CodeMarker01/do-an-1-b/Design Hardware/Design/Schematic.jpg

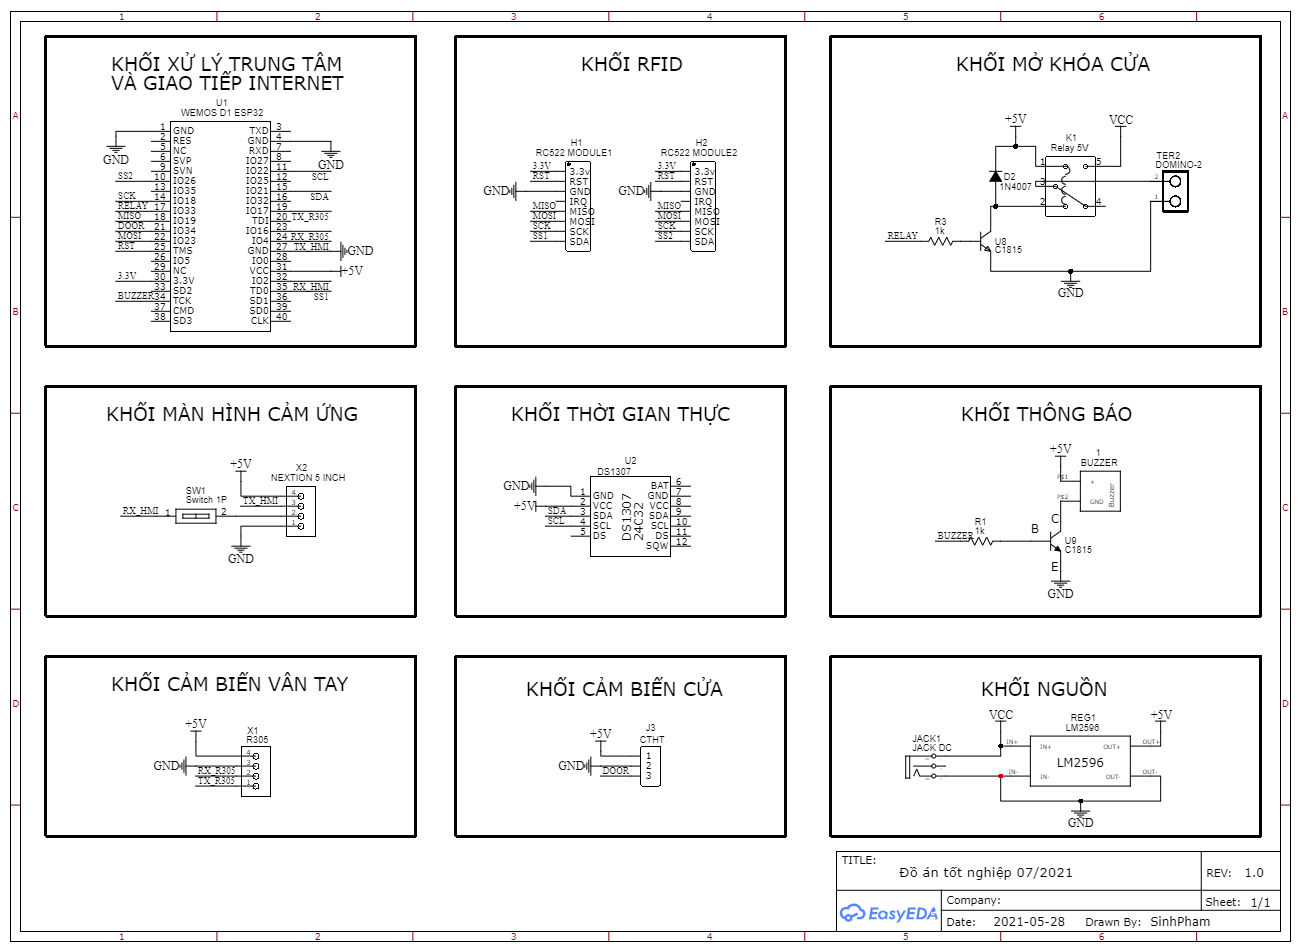
Design Hardware/Design/Schematic.jpg
