CodeMarker01/do-an-1-b/Design Hardware/Image/Actual image/z2544615937646_9335fb49bdb557f8bc9e90b8a1676609.jpg

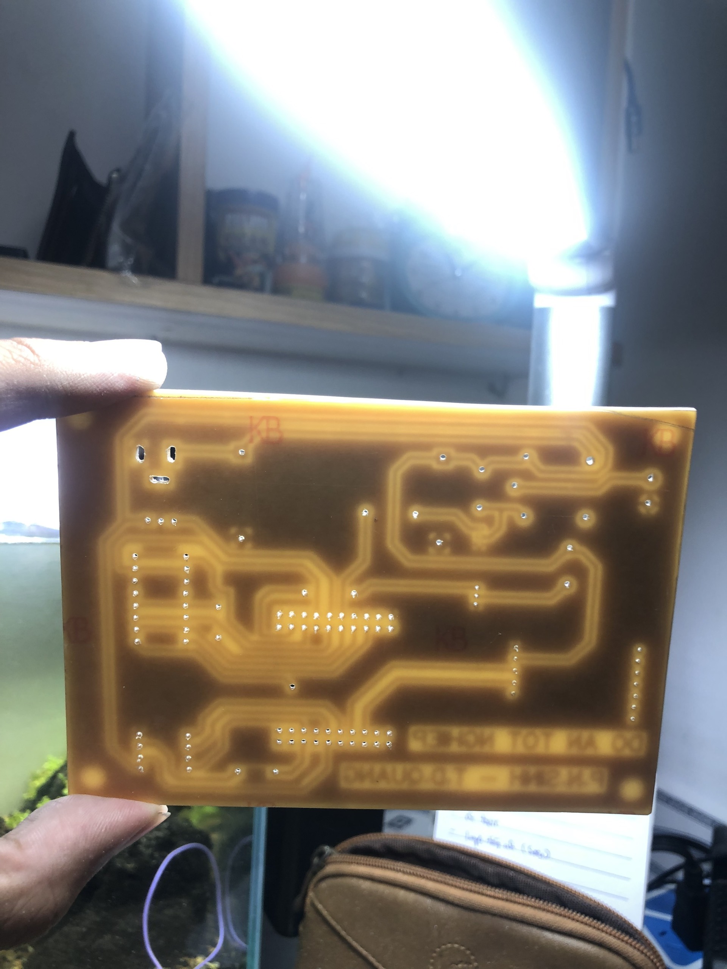
Design Hardware/Image/Actual image/z2544615937646_9335fb49bdb557f8bc9e90b8a1676609.jpg
