CodeMarker01/do-an-1-b/Design Hardware/Image/Actual image/z2544616110055_0c806b30d1a9bc31b851866c3de1ba1b.jpg

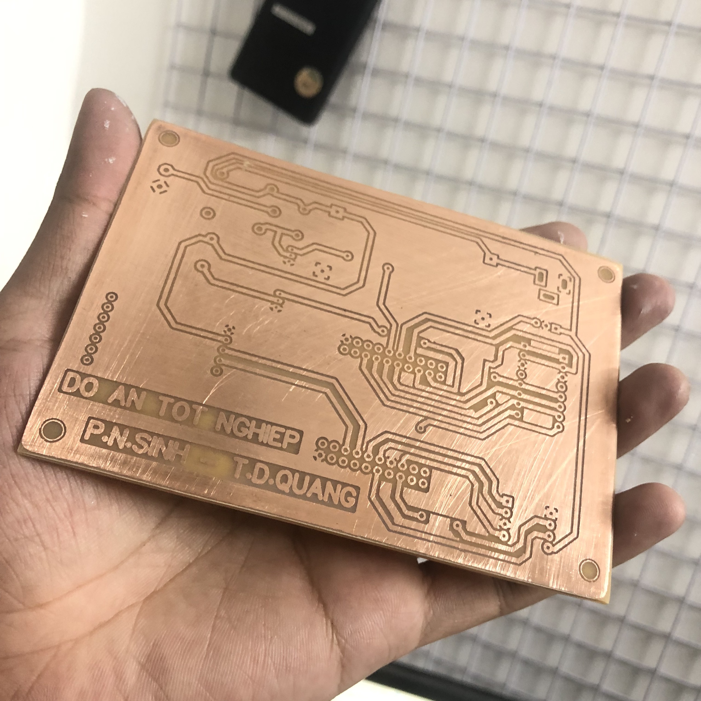
Design Hardware/Image/Actual image/z2544616110055_0c806b30d1a9bc31b851866c3de1ba1b.jpg
