CodeMarker01/do-an-1-b/Design Hardware/Image/Actual image/z2544616175655_86c2982712d3af7087d2432e3efe20b5.jpg

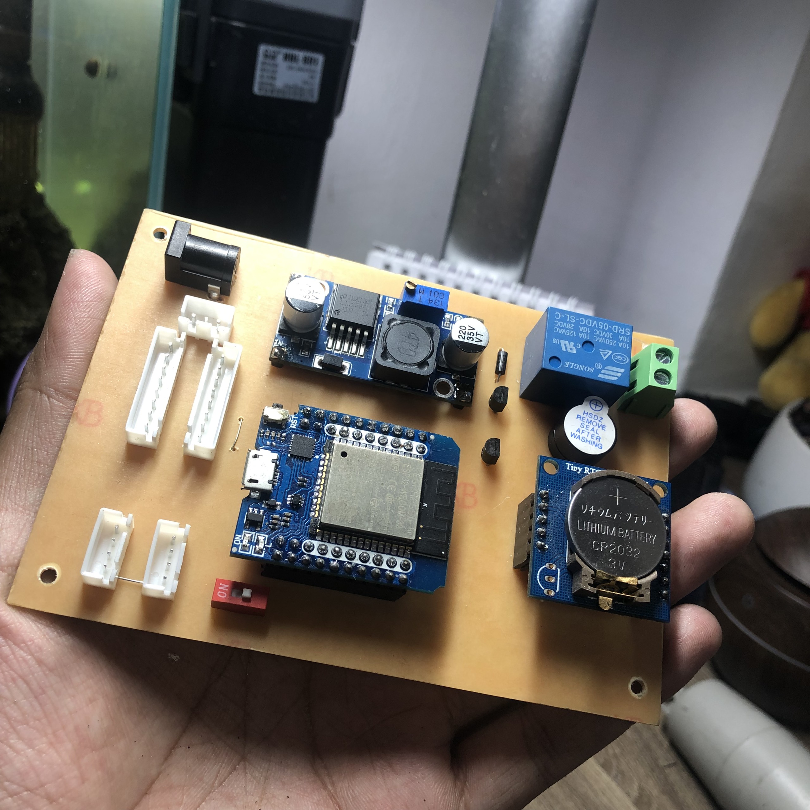
Design Hardware/Image/Actual image/z2544616175655_86c2982712d3af7087d2432e3efe20b5.jpg
