CodeMarker01/do-an-1-b/Design Hardware/Image/Actual image/z2544616294131_eab570bc93009f2e7a02063649fb9a35.jpg

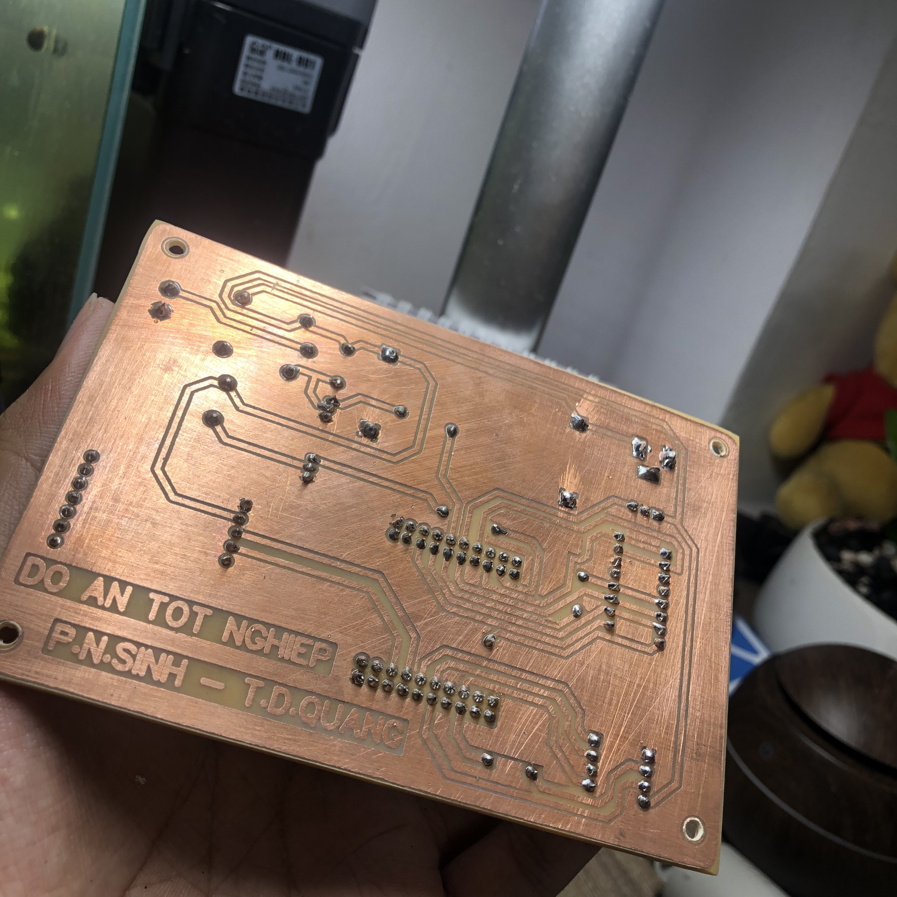
Design Hardware/Image/Actual image/z2544616294131_eab570bc93009f2e7a02063649fb9a35.jpg
