CodeMarker01/do-an-1-b/Design Hardware/Image/Actual image/z2544616418937_9a0d63e0b6e5f737682f1ef8a417e20c.jpg

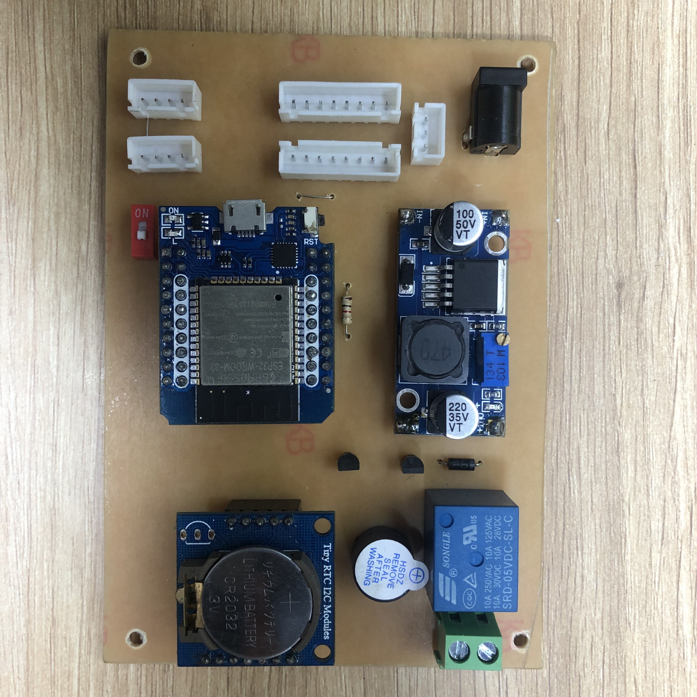
Design Hardware/Image/Actual image/z2544616418937_9a0d63e0b6e5f737682f1ef8a417e20c.jpg
