CodeMarker01/do-an-1-b/Design Hardware/Image/Actual image/z2544616560953_9db783ca1c101b86c6ae915941142b20.jpg

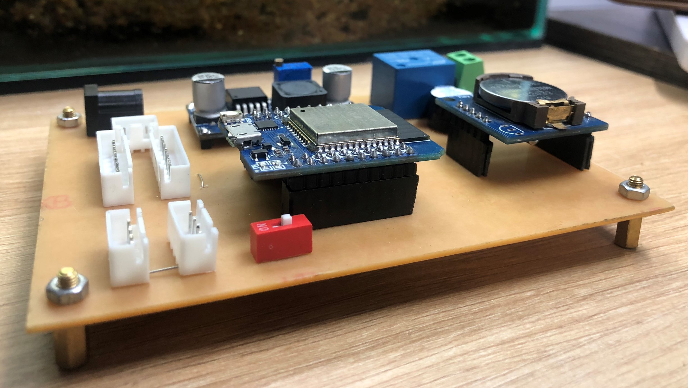
Design Hardware/Image/Actual image/z2544616560953_9db783ca1c101b86c6ae915941142b20.jpg
