CodeMarker01/do-an-1-b/Design Hardware/Image/Actual image/z2544616626180_2d66d4fd1934191050b84d0e8d568436.jpg

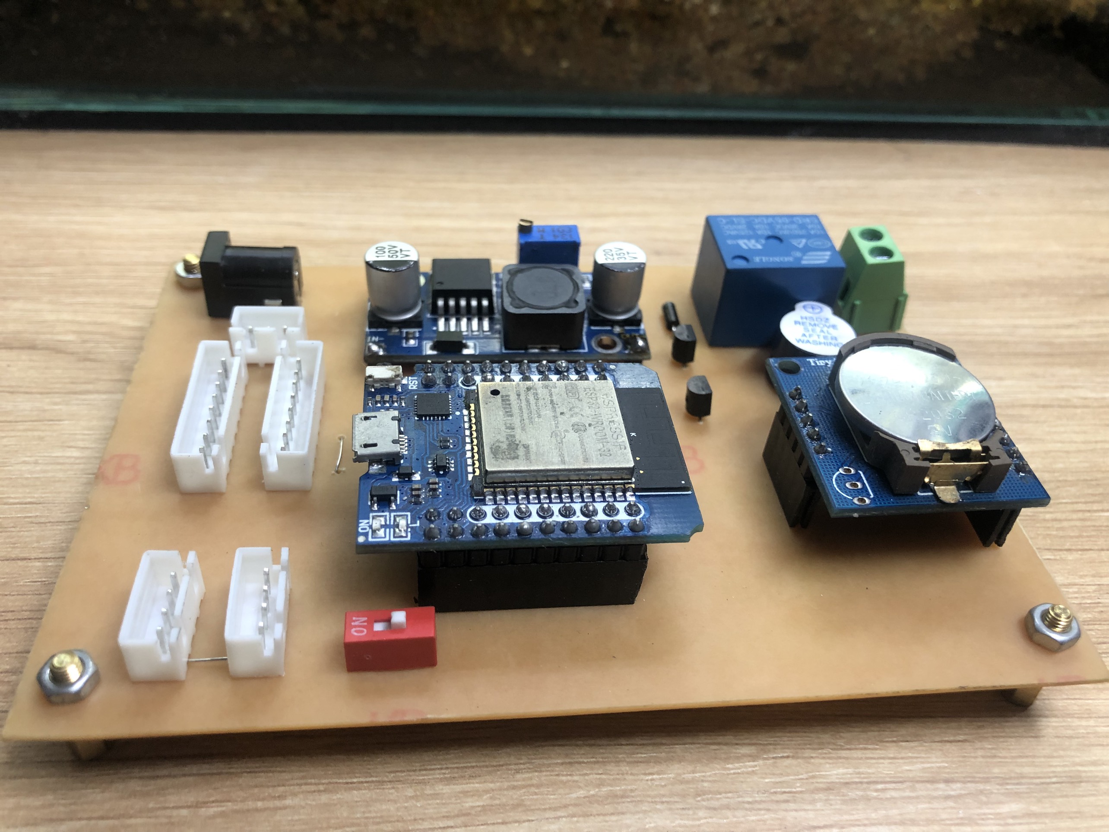
Design Hardware/Image/Actual image/z2544616626180_2d66d4fd1934191050b84d0e8d568436.jpg
