CodeMarker01/do-an-1-b/Design Hardware/Image/Actual image/z2544616677354_602826e0f4558f78ebcde85a3f661dc7.jpg

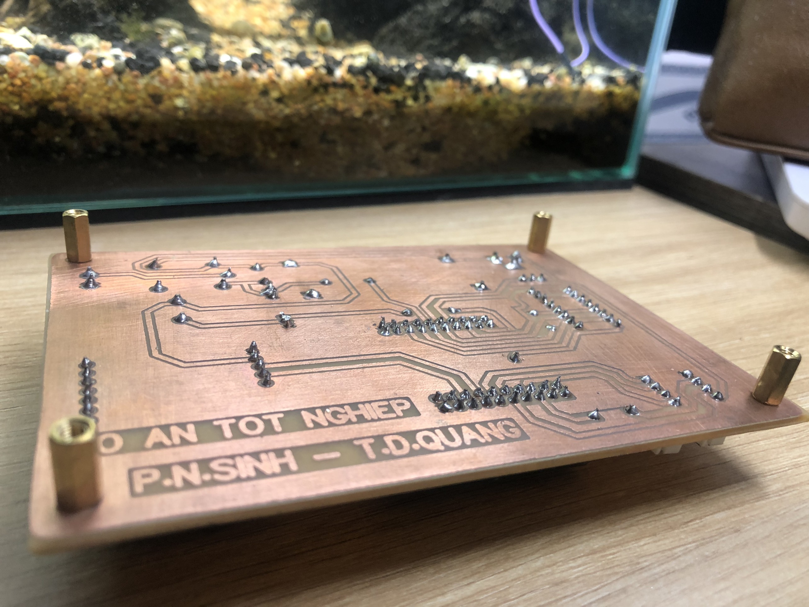
Design Hardware/Image/Actual image/z2544616677354_602826e0f4558f78ebcde85a3f661dc7.jpg
