CodeMarker01/do-an-1-b/Design Hardware/Image/Actual image/z2544616764803_e4a6f4069bfe7fa6eb25443e5bb9a443.jpg

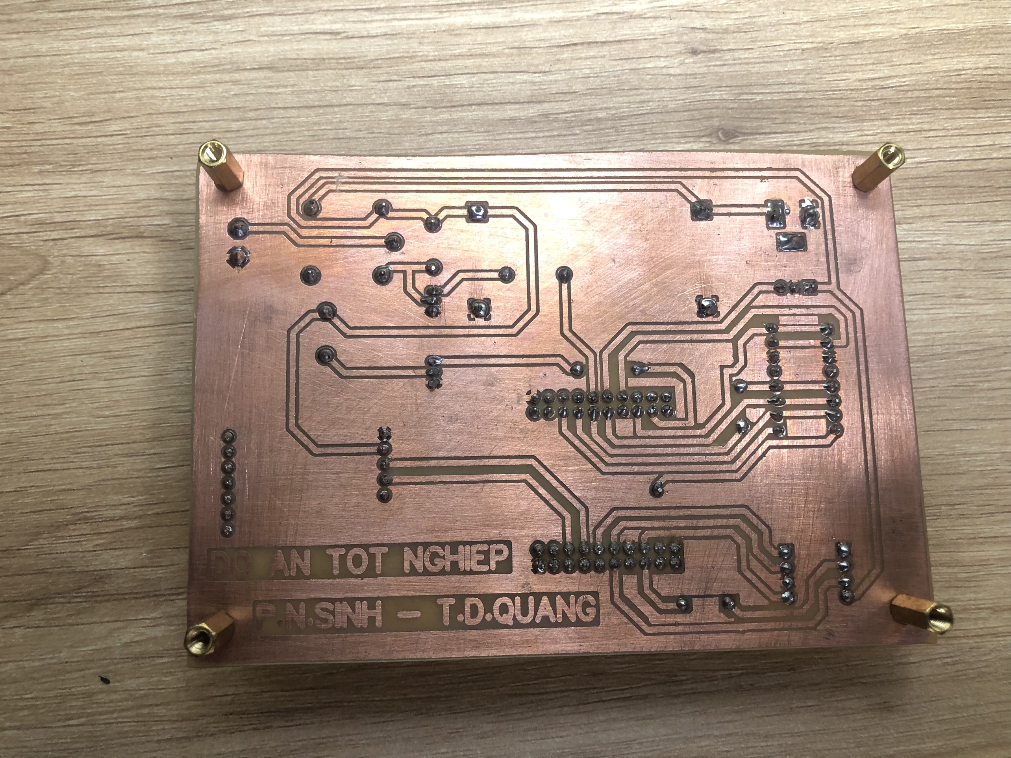
Design Hardware/Image/Actual image/z2544616764803_e4a6f4069bfe7fa6eb25443e5bb9a443.jpg
