CodeMarker01/do-an-1-b/Design Hardware/Image/Actual image/z2544616827099_3f5eeda9f5f875da7b8a4e99138490a9.jpg

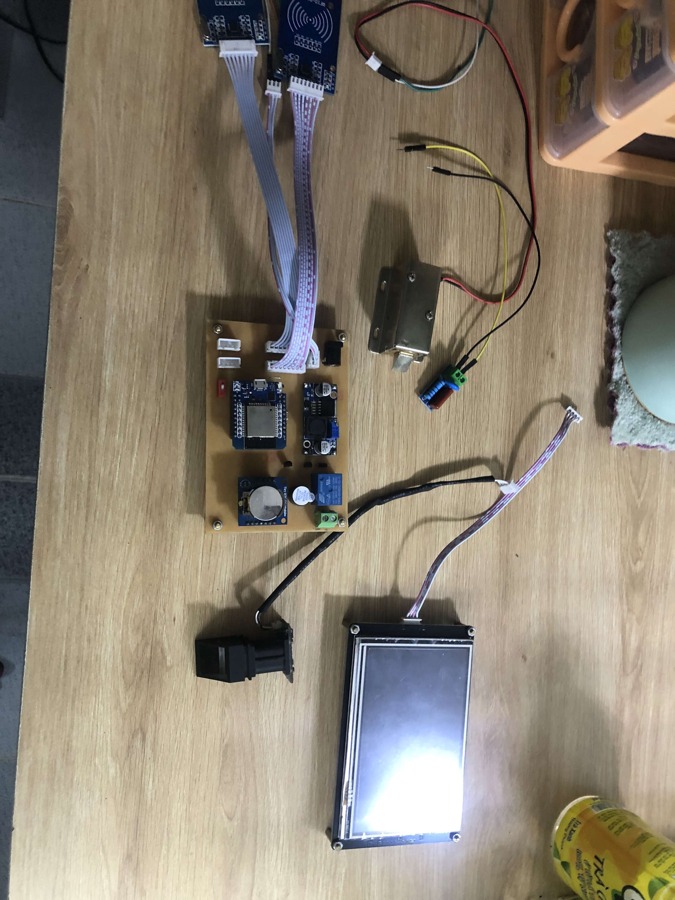
Design Hardware/Image/Actual image/z2544616827099_3f5eeda9f5f875da7b8a4e99138490a9.jpg
