CodeMarker01/do-an-1-b/Design Hardware/Image/Simulation image/2D_TOP.png

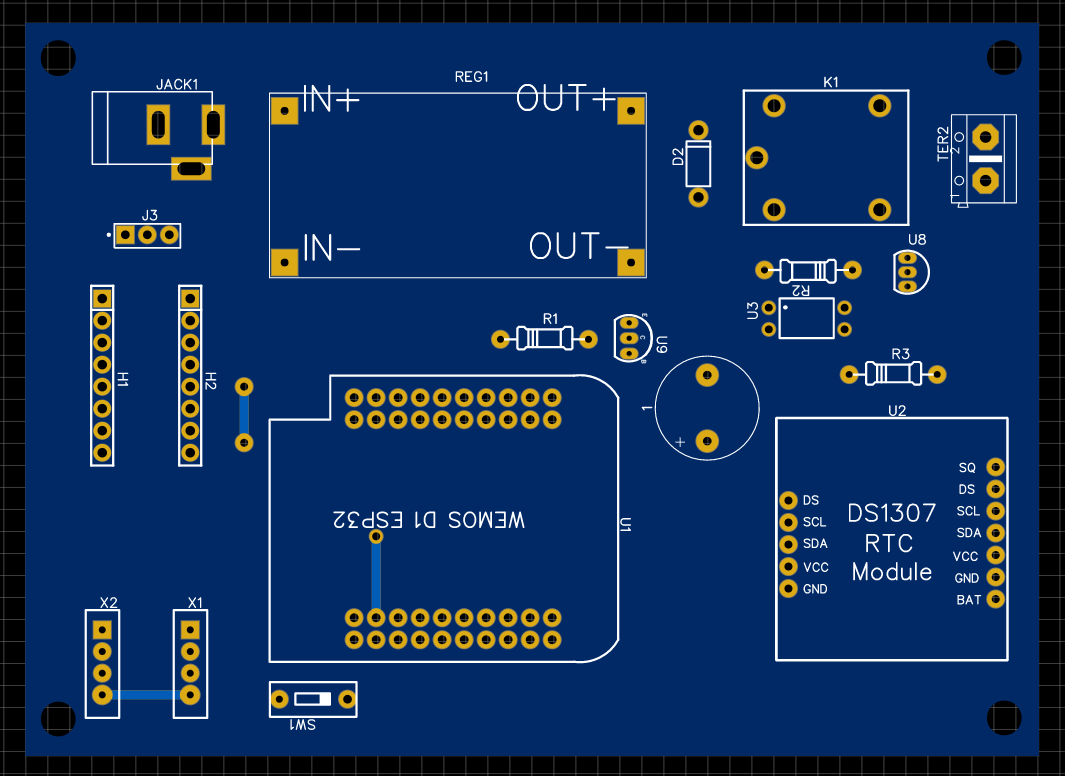
Design Hardware/Image/Simulation image/2D_TOP.png
