CodeMarker01/do-an-1-b/Design Hardware/Image/Simulation image/3D_BOTTOM.png

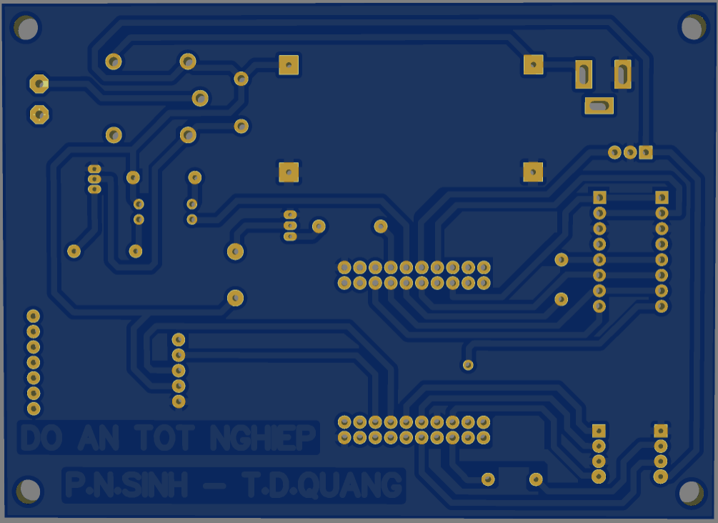
Design Hardware/Image/Simulation image/3D_BOTTOM.png
