CodeMarker01/do-an-1-b/Design Hardware/Image/Simulation image/SIZE.png

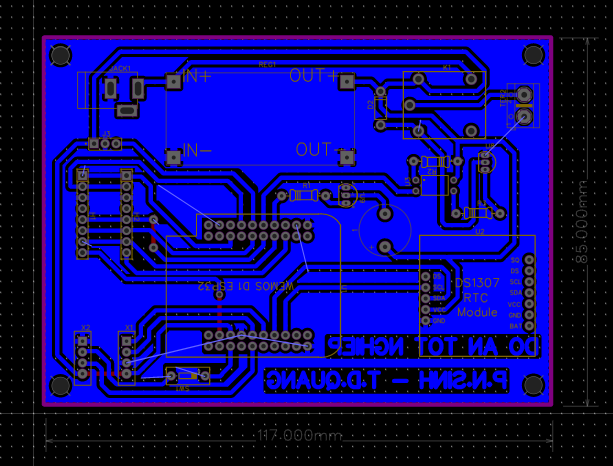
Design Hardware/Image/Simulation image/SIZE.png
