CodeMarker01/do-an-1-b/Design Hardware/Image/Simulation image/TopLayyer.png

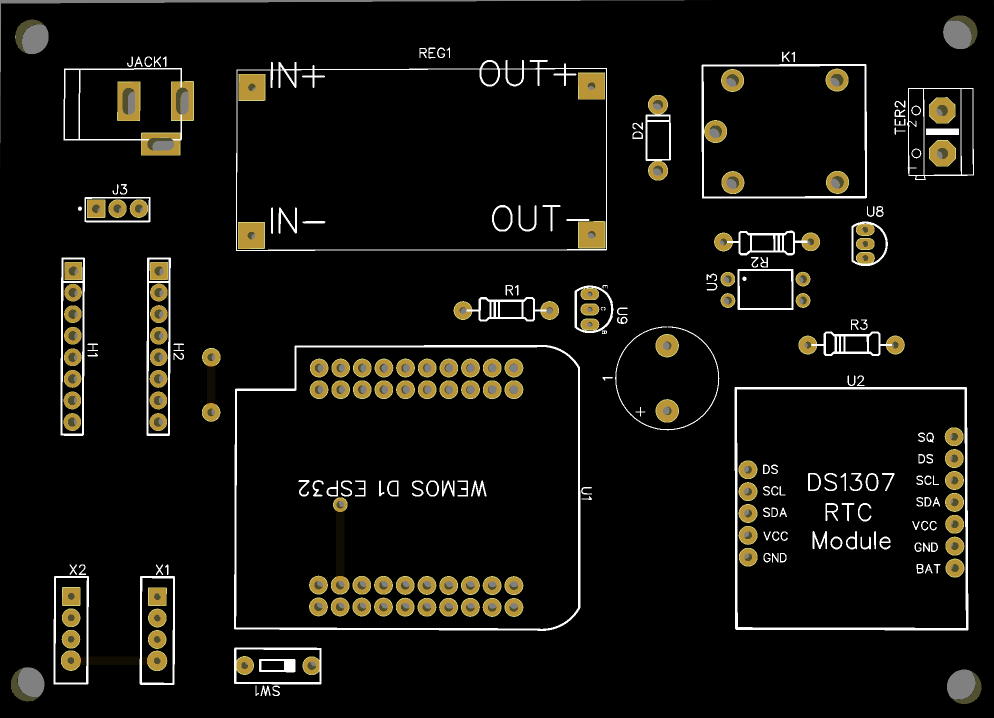
Design Hardware/Image/Simulation image/TopLayyer.png
