CodeMarker01/do-an-1-b/Design HMI/Picture/a/SPKT.jpg

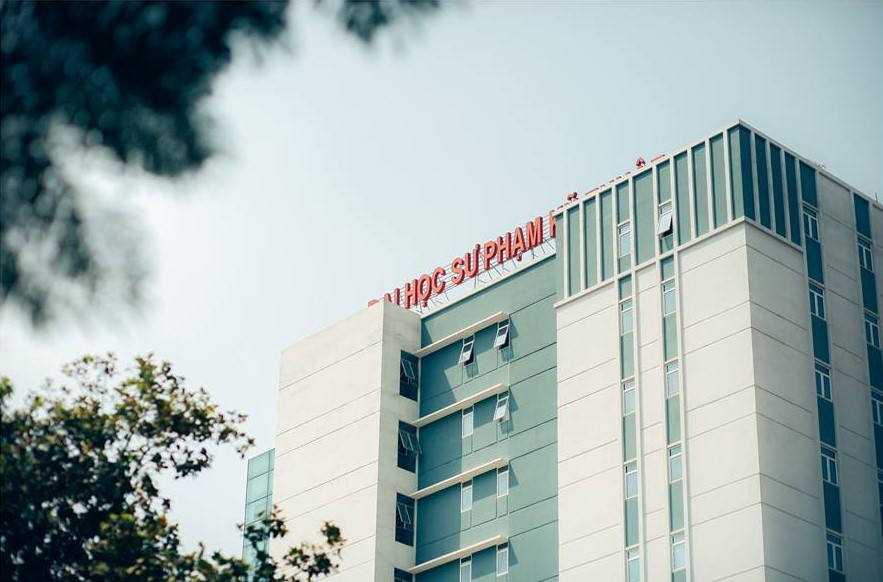
Design HMI/Picture/a/SPKT.jpg
