CodeMarker01/do-an-1-b/Design HMI/Picture/a/SS2.jpg

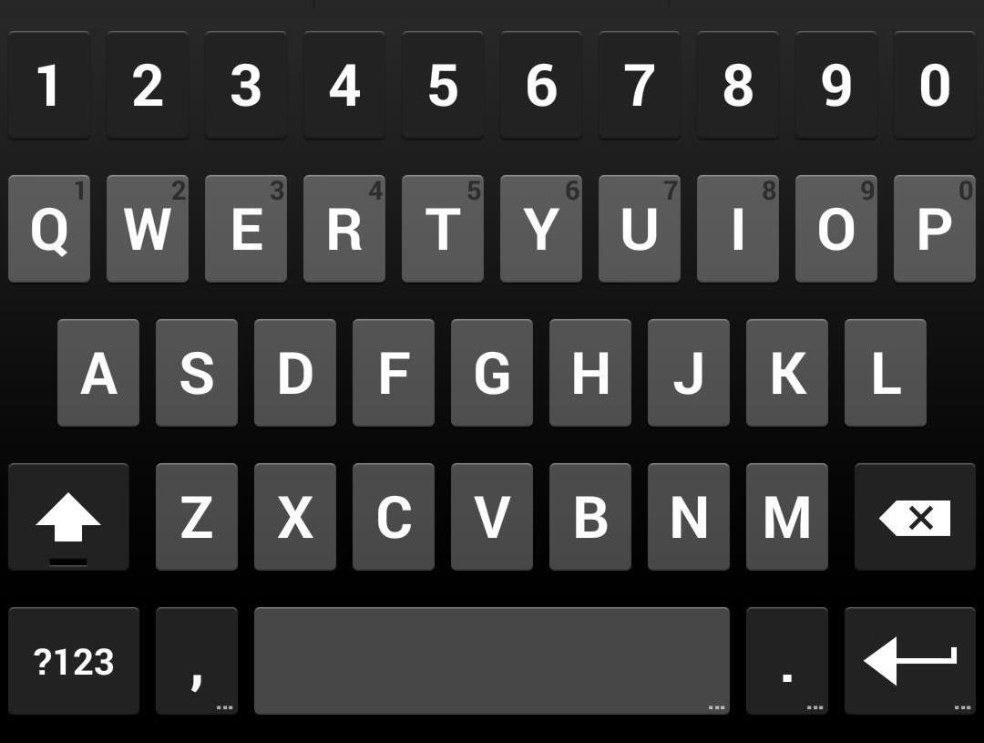
Design HMI/Picture/a/SS2.jpg
