CodeMarker01/do-an-1-b/Design HMI/Picture/a/UTE/SPKT3.jpg

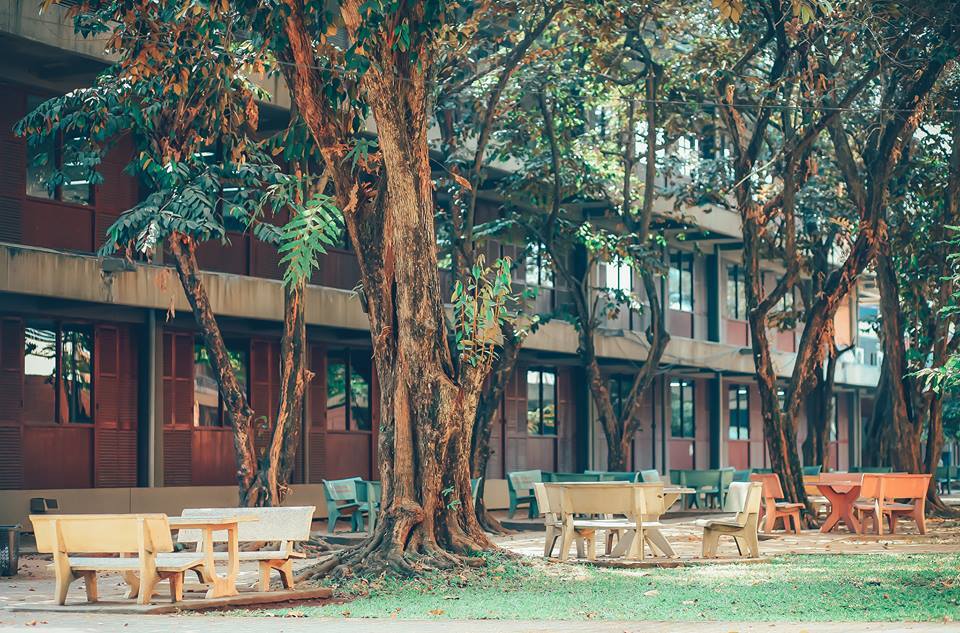
Design HMI/Picture/a/UTE/SPKT3.jpg
