CodeMarker01/do-an-1-b/Design HMI/Picture/a/UTE/SPKT4.jpg

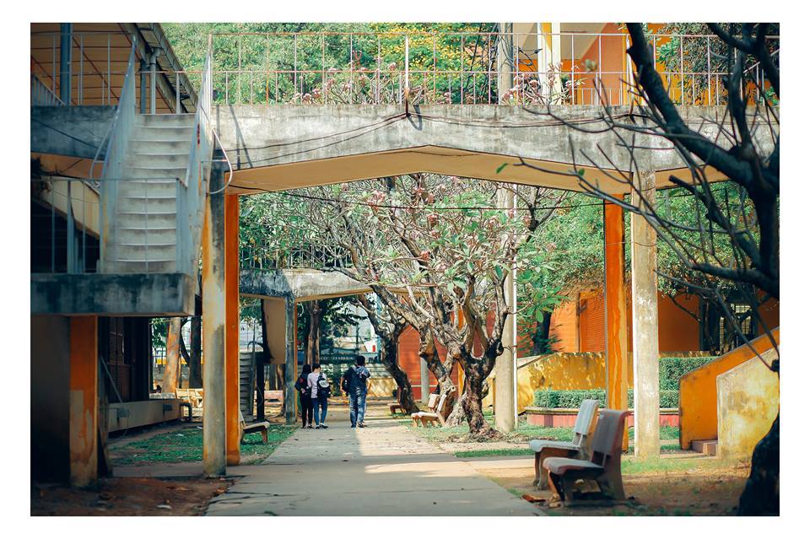
Design HMI/Picture/a/UTE/SPKT4.jpg
