CodeMarker01/do-an-1-b/Design HMI/Picture/a/UTE/SPKT_CONG.jpg

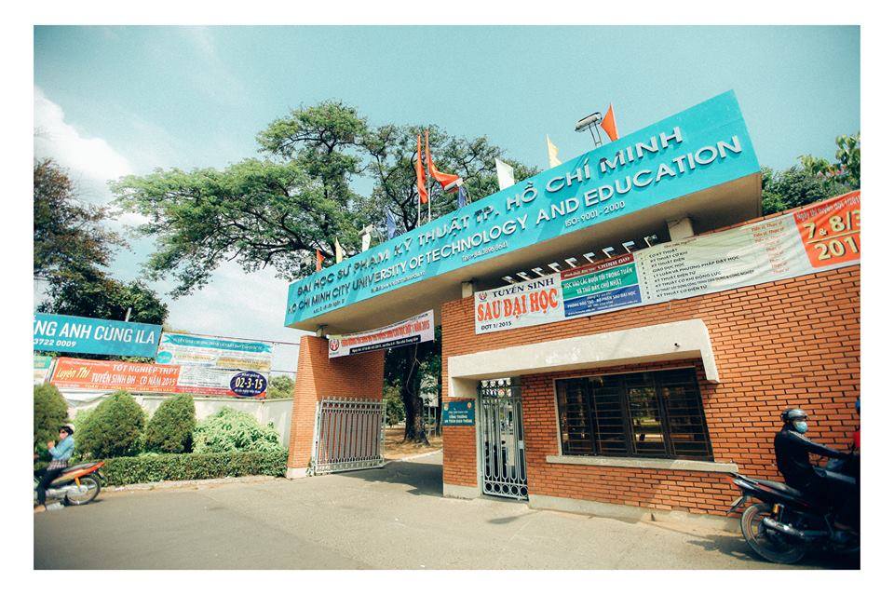
Design HMI/Picture/a/UTE/SPKT_CONG.jpg
