CodeMarker01/do-an-1-b/Design HMI/Picture/b/9.png

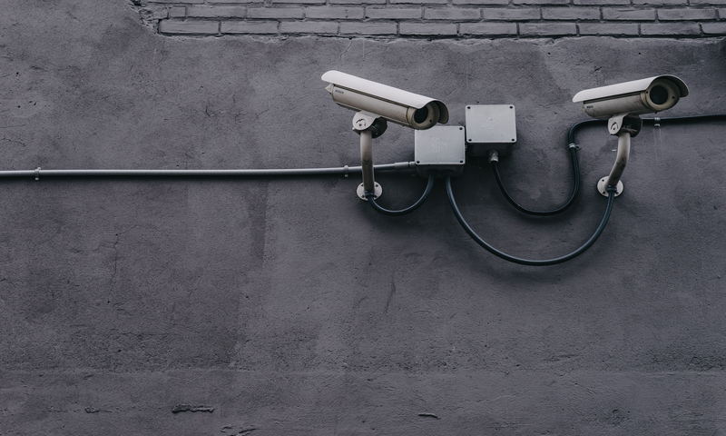
Design HMI/Picture/b/9.png
