CodeMarker01/do-an-1-b/Design HMI/Picture/b/13.png

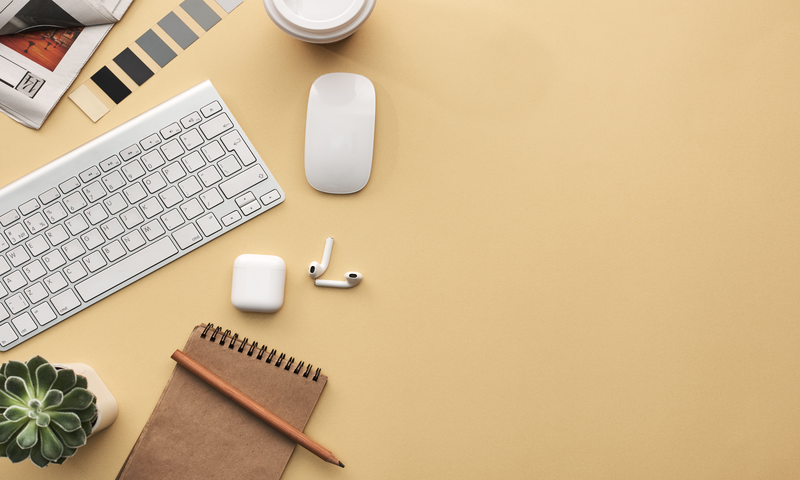
Design HMI/Picture/b/13.png
