CodeMarker01/do-an-1-b/Design HMI/Picture/b/keyboard.png

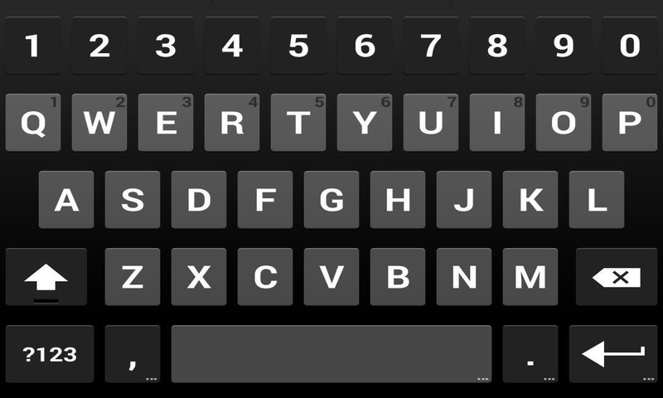
Design HMI/Picture/b/keyboard.png
