CodeMarker01/do-an-1-b/Design Model/3D/Hộp 1.jpg

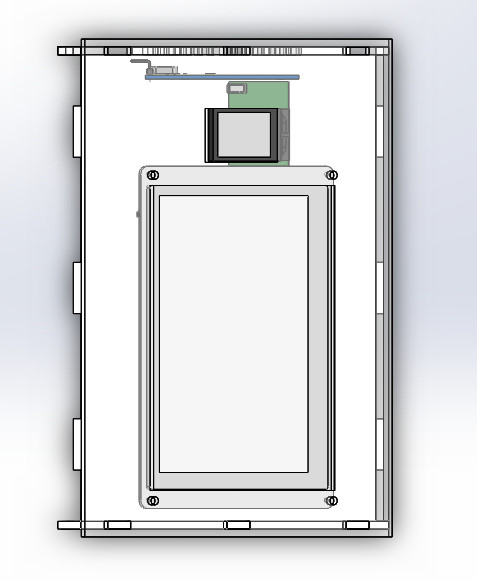
Design Model/3D/Hộp 1.jpg
