CodeMarker01/do-an-1-b/Design Model/3D/Hộp 2.jpg

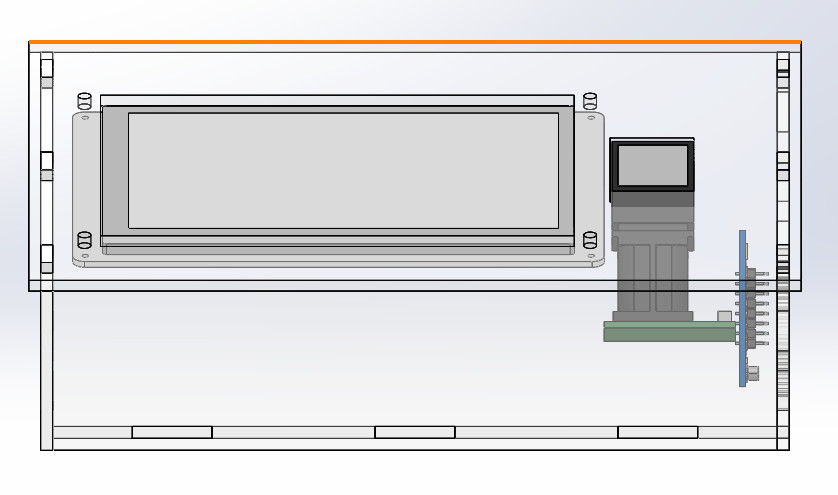
Design Model/3D/Hộp 2.jpg
