CodeMarker01/do-an-1-b/Design Model/3D/Hộp 3.jpg

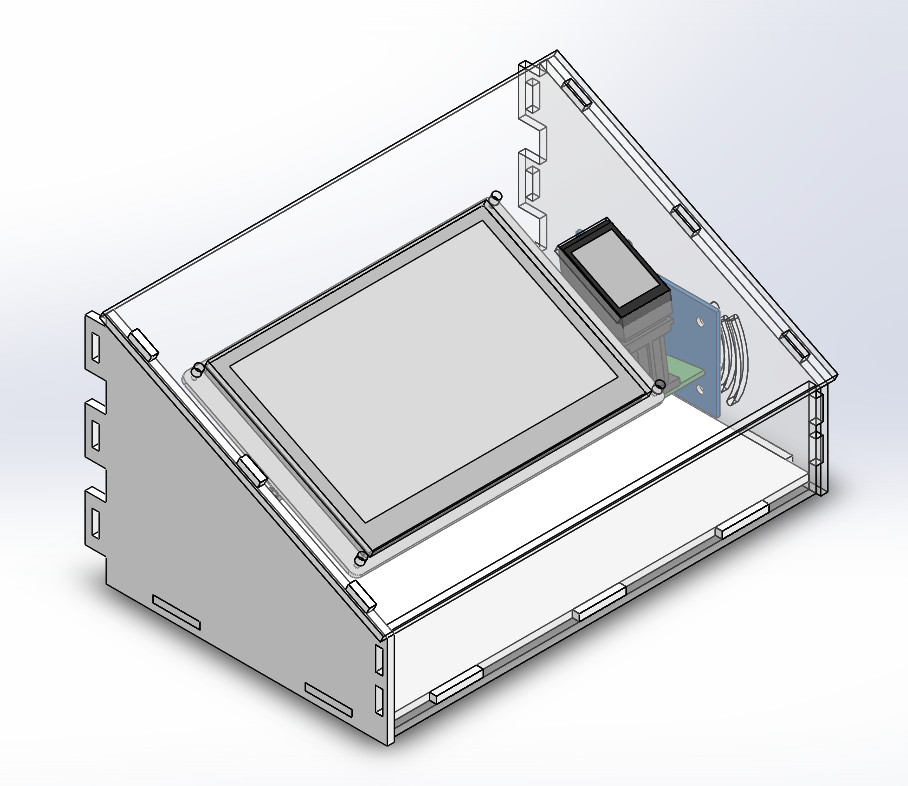
Design Model/3D/Hộp 3.jpg
