CodeMarker01/do-an-1-b/Design Model/3D/Simulation2.jpg

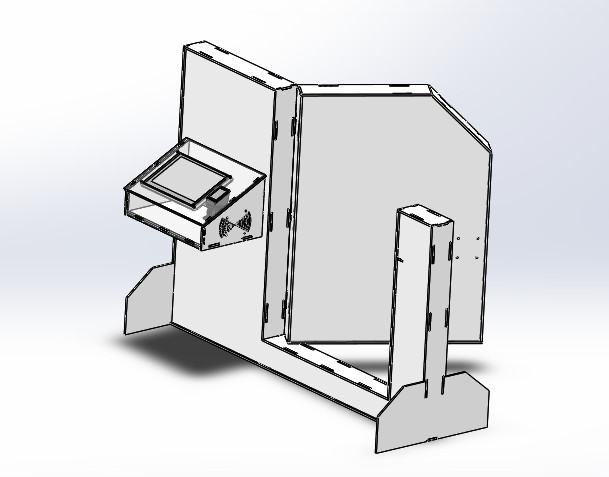
Design Model/3D/Simulation2.jpg
