CodeMarker01/do-an-1-b/Design Model/3D/Simulation4.jpg

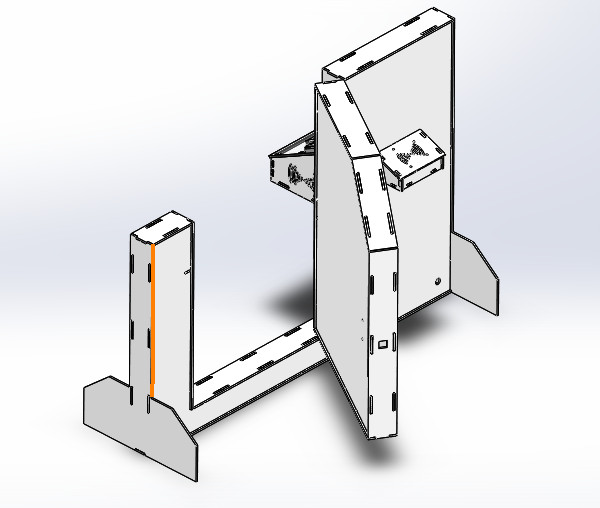
Design Model/3D/Simulation4.jpg
