CodeMarker01/do-an-1-b/Design Model/Autocad/New folder/Size Module/Chốt điện 12v.jpg

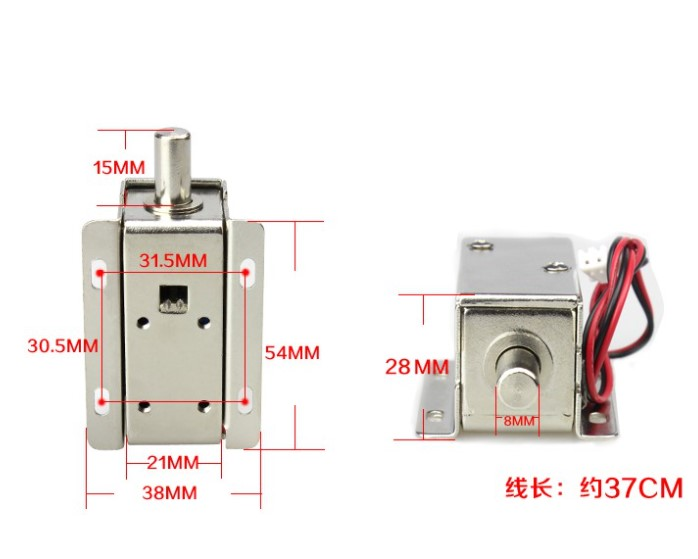
Design Model/Autocad/New folder/Size Module/Chốt điện 12v.jpg
