CodeMarker01/do-an-1-b/Design Model/Autocad/New folder/Size Module/Công tắt hành trình.jpg

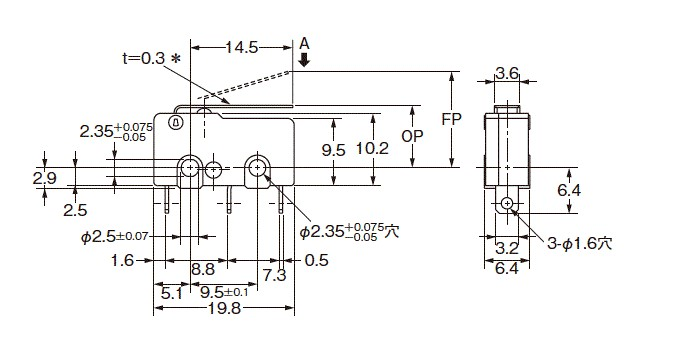
Design Model/Autocad/New folder/Size Module/Công tắt hành trình.jpg
