CodeMarker01/do-an-1-b/Design Model/Autocad/New folder/Size Module/Cảm biến vân tay R305.jpg

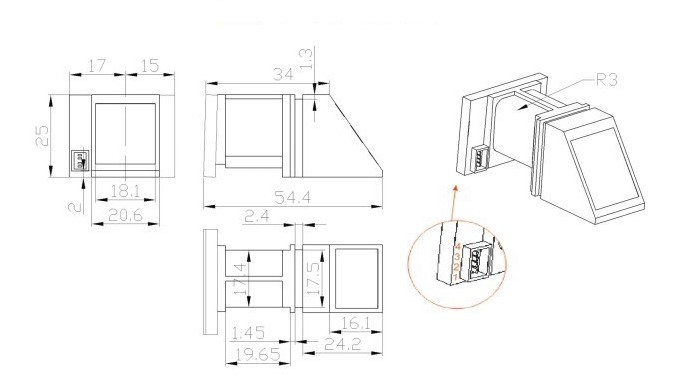
Design Model/Autocad/New folder/Size Module/Cảm biến vân tay R305.jpg
