CodeMarker01/do-an-1-b/Design Model/Autocad/New folder/Size Module/Nextion 5inch.jpg

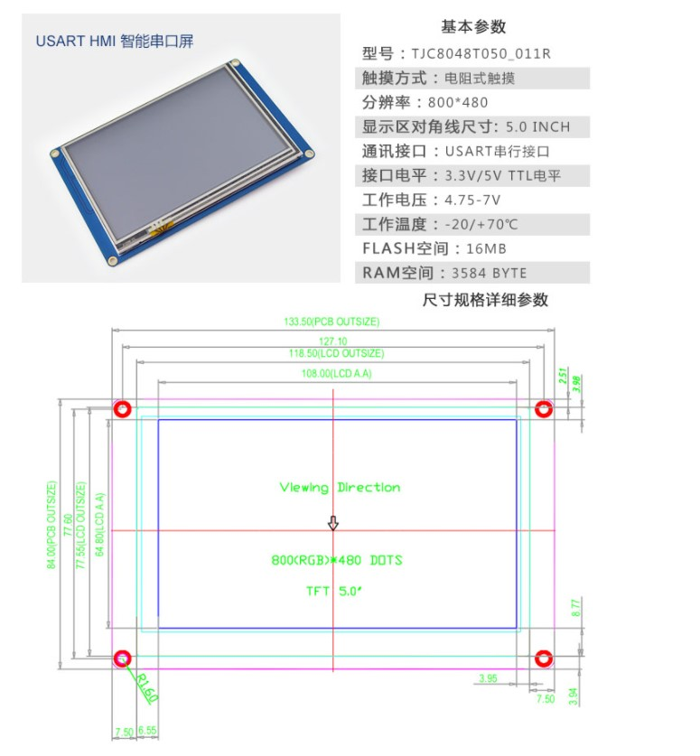
Design Model/Autocad/New folder/Size Module/Nextion 5inch.jpg
