CodeMarker01/do-an-1-b/Design Model/Autocad/New folder/Size Module/RFID.jpg

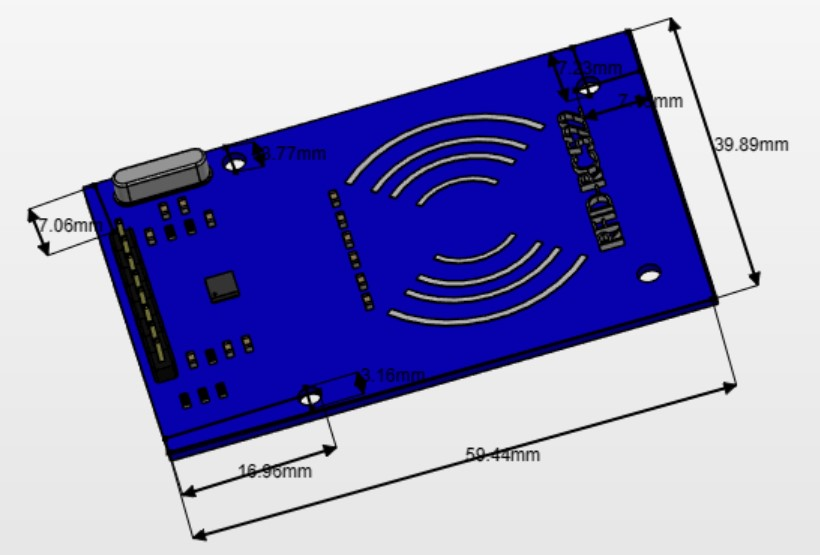
Design Model/Autocad/New folder/Size Module/RFID.jpg
