CodeMarker01/do-an-1-b/Design Model/Size Module/File 3D module/Picture/12V DC Electrical Interlock.JPG

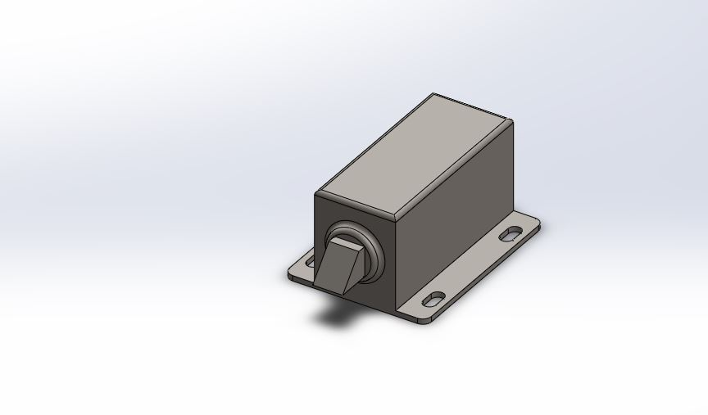
Design Model/Size Module/File 3D module/Picture/12V DC Electrical Interlock.JPG
