CodeMarker01/do-an-1-b/Design Model/Size Module/File 3D module/Picture/fingerprint sensor.jpg

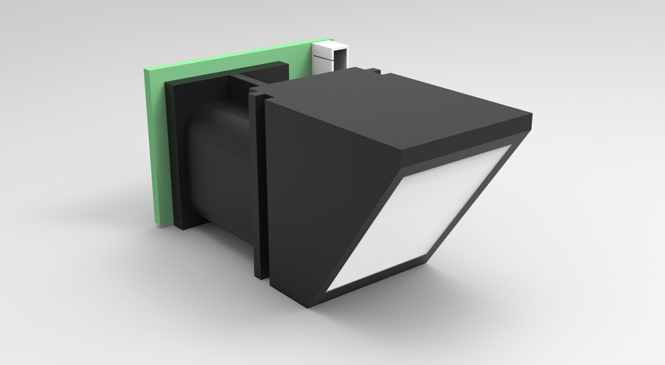
Design Model/Size Module/File 3D module/Picture/fingerprint sensor.jpg
