CodeMarker01/do-an-1-b/Embedded/Code/DEFINE_PIN.png

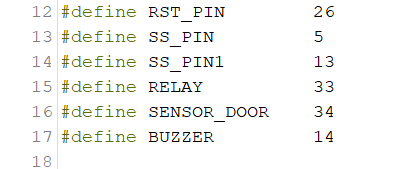
Embedded/Code/DEFINE_PIN.png
