CodeMarker01/do-an-1-b/Design Model/Autocad/Khungcua_vachtren.SLDPRT

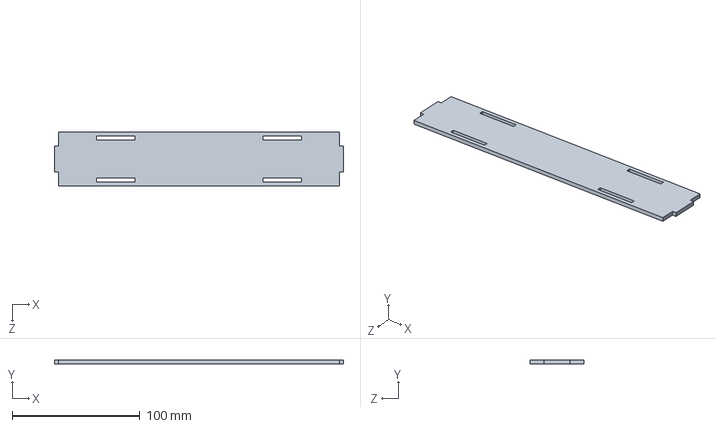
[picture p76: CAD file, 2021-06-23]
Design Model/Autocad/Khungcua_vachtren.SLDPRT
226.0 x 3.00 x 42.0 mm
