CodeMarker01/do-an-1-b/Design Model/Autocad/cua_vachtren1.SLDPRT

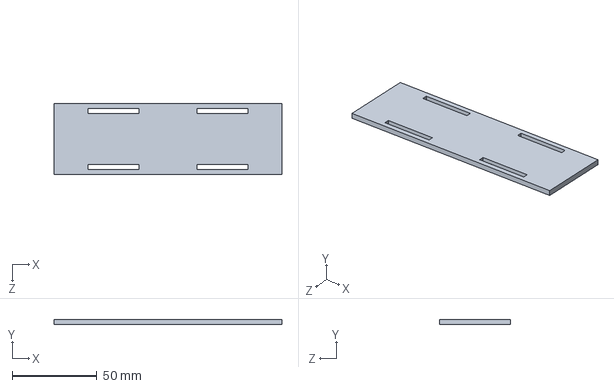
[picture p77: CAD file, 2021-06-23]
Design Model/Autocad/cua_vachtren1.SLDPRT
134.4 x 3.00 x 42.0 mm
