CodeMarker01/do-an-1-b/Design Model/Autocad/H_mattruoc.SLDPRT

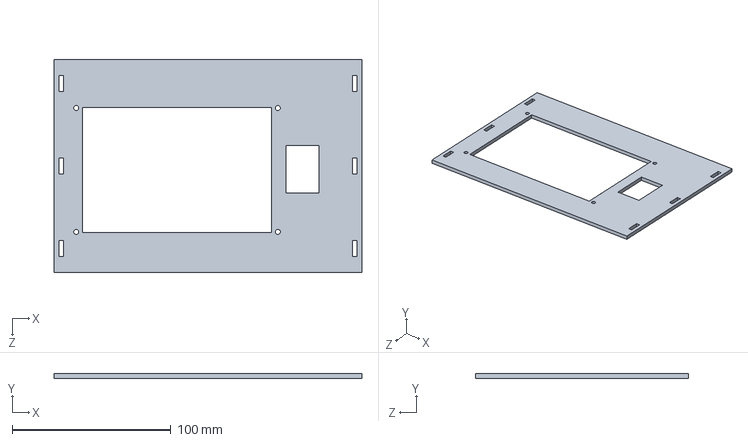
[picture p78: CAD file, 2021-06-23]
Design Model/Autocad/H_mattruoc.SLDPRT
194.0 x 3.00 x 134.0 mm
