CodeMarker01/do-an-1-b/Design Model/Autocad/HOPRFID_vachtruoc.SLDPRT

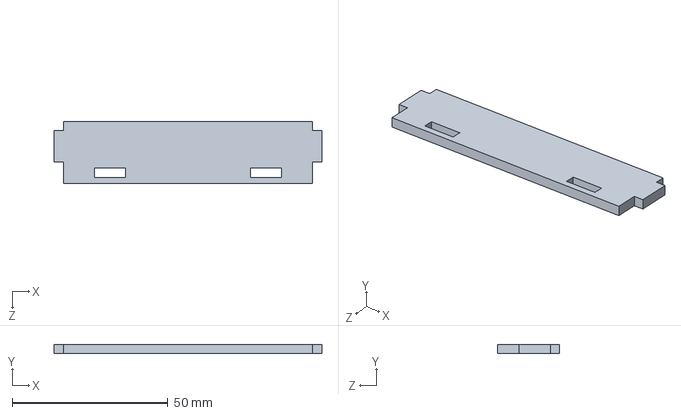
[picture p79: CAD file, 2021-06-23]
Design Model/Autocad/HOPRFID_vachtruoc.SLDPRT
86.0 x 3.00 x 20.0 mm
