CodeMarker01/do-an-1-b/Design Model/Autocad/Khungcua_vachsau.SLDPRT

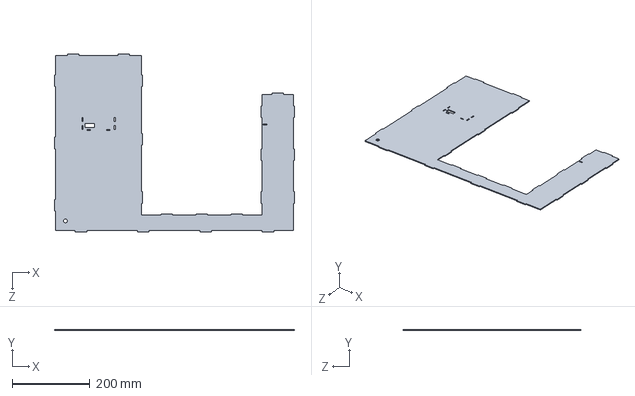
[picture p80: CAD file, 2021-06-23]
Design Model/Autocad/Khungcua_vachsau.SLDPRT
616.0 x 2.50 x 456.0 mm
