CodeMarker01/do-an-1-b/Design Model/Autocad/Khungcua_vachtruoc.SLDPRT

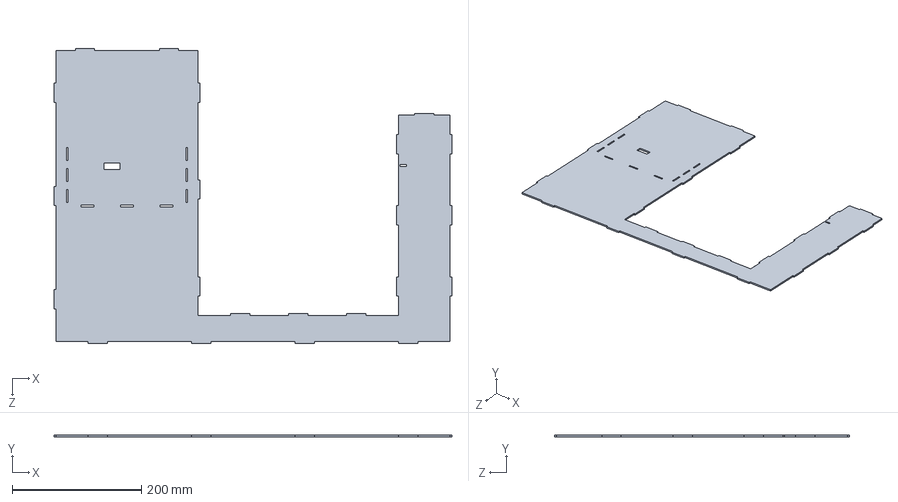
[picture p81: CAD file, 2021-06-23]
Design Model/Autocad/Khungcua_vachtruoc.SLDPRT
616.0 x 3.00 x 456.0 mm
