CodeMarker01/do-an-1-b/Design Model/Autocad/H_mathongphai.SLDPRT

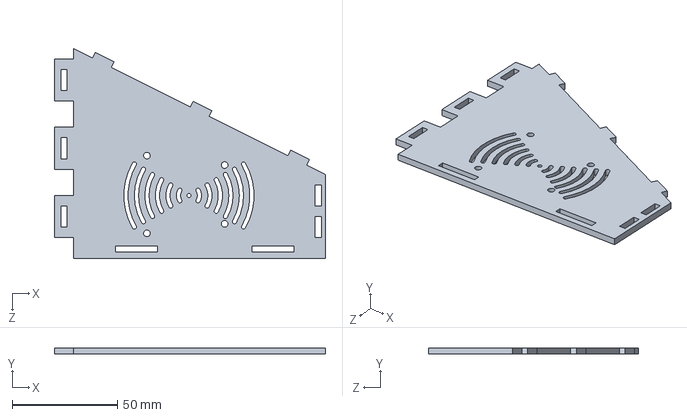
[picture p82: CAD file, 2021-06-23]
Design Model/Autocad/H_mathongphai.SLDPRT
129.0 x 3.00 x 100.0 mm
