CodeMarker01/do-an-1-b/Design Model/Autocad/cua_vachtrai.SLDPRT

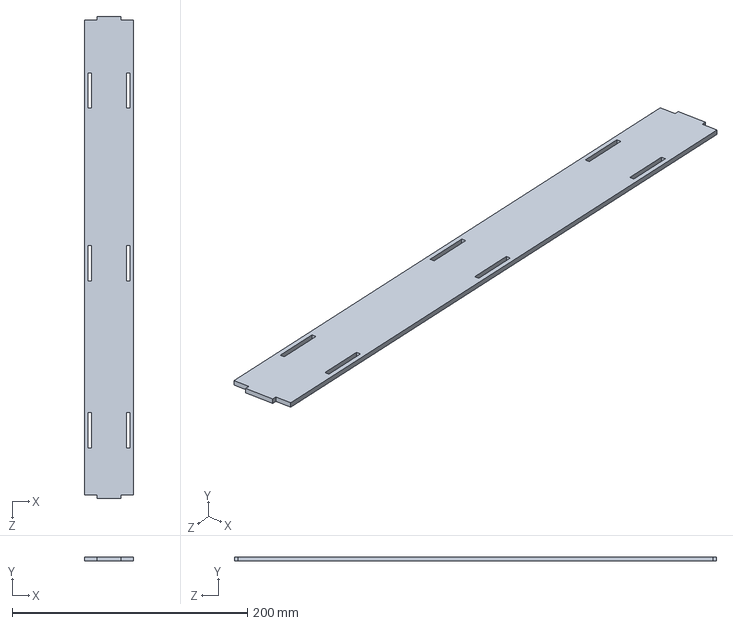
[picture p83: CAD file, 2021-06-23]
Design Model/Autocad/cua_vachtrai.SLDPRT
42.0 x 3.00 x 410.0 mm
