CodeMarker01/do-an-1-b/Design Model/Autocad/H_matday.SLDPRT

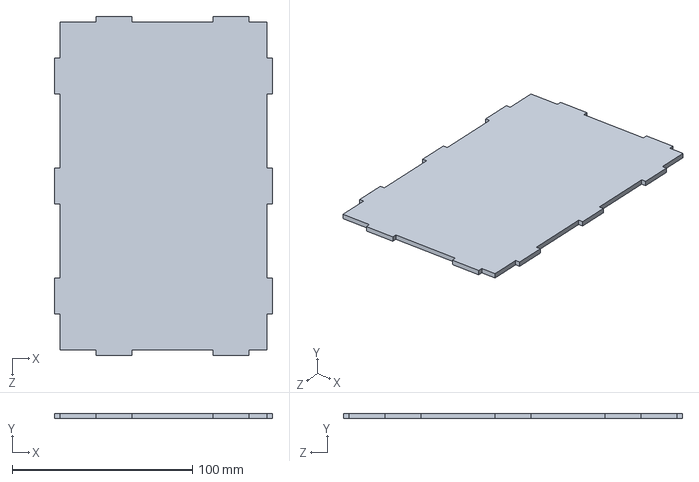
[picture p84: CAD file, 2021-06-23]
Design Model/Autocad/H_matday.SLDPRT
121.0 x 3.00 x 188.0 mm
