CodeMarker01/do-an-1-b/Design Model/Autocad/Khungcua_vachtrennho.SLDPRT

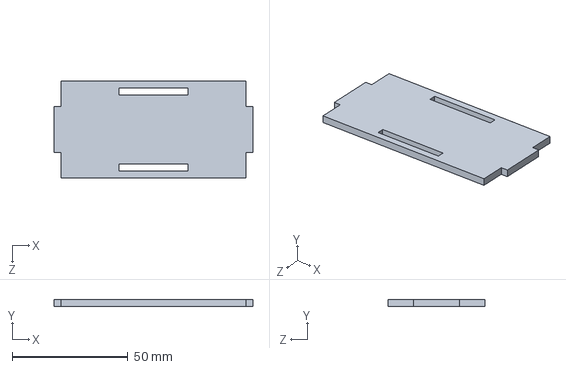
[picture p85: CAD file, 2021-06-23]
Design Model/Autocad/Khungcua_vachtrennho.SLDPRT
86.0 x 3.00 x 42.0 mm
