CodeMarker01/do-an-1-b/Design Model/Autocad/HOPRFID_vachtren.SLDPRT

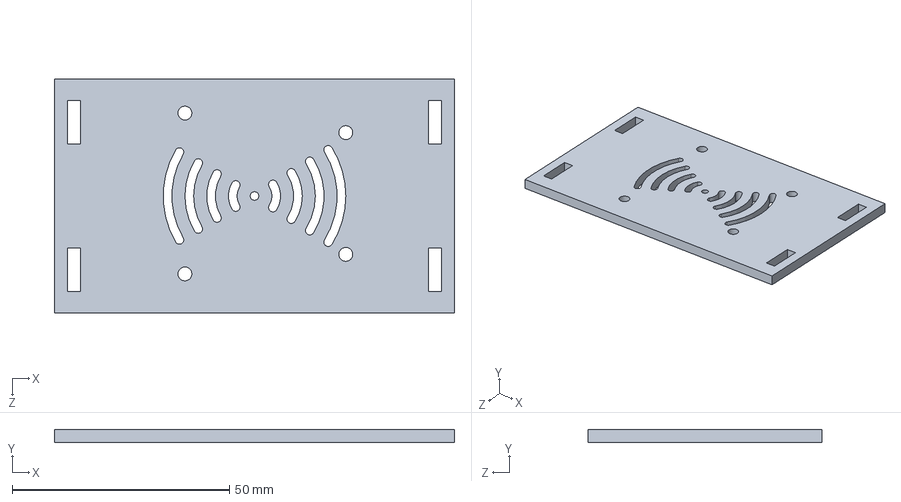
[picture p87: CAD file, 2021-06-23]
Design Model/Autocad/HOPRFID_vachtren.SLDPRT
92.0 x 3.00 x 53.8 mm
