CodeMarker01/do-an-1-b/Design Model/Autocad/H_matdoidien.SLDPRT

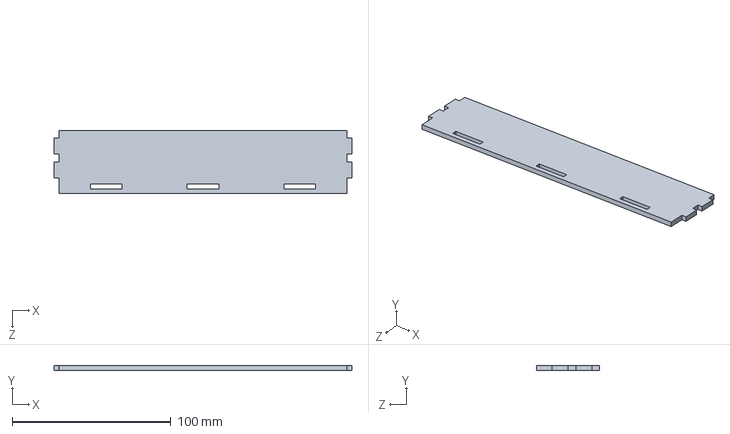
[picture p88: CAD file, 2021-06-23]
Design Model/Autocad/H_matdoidien.SLDPRT
188.0 x 3.00 x 40.0 mm
