CodeMarker01/do-an-1-b/Design Model/Autocad/Khungcua_vachday.SLDPRT

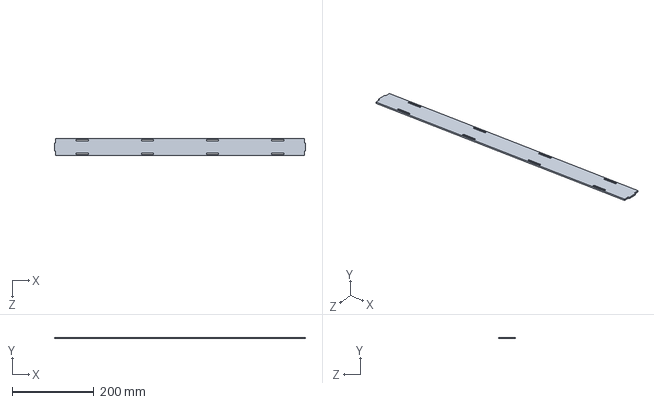
[picture p89: CAD file, 2021-06-23]
Design Model/Autocad/Khungcua_vachday.SLDPRT
616.0 x 3.00 x 42.0 mm
