CodeMarker01/do-an-1-b/Design Model/Autocad/cua_vachday.SLDPRT

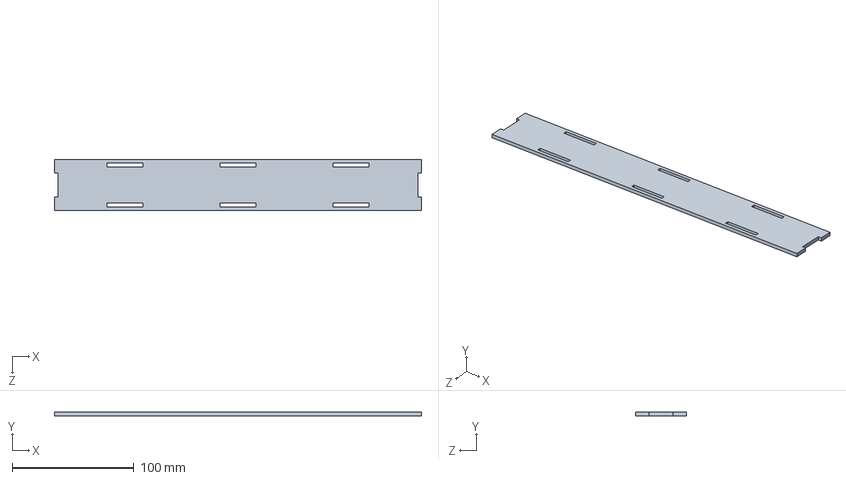
[picture p90: CAD file, 2021-06-23]
Design Model/Autocad/cua_vachday.SLDPRT
302.0 x 3.00 x 42.0 mm
