CodeMarker01/do-an-1-b/Design Model/Autocad/Khungcua_vachhongtrai.SLDPRT

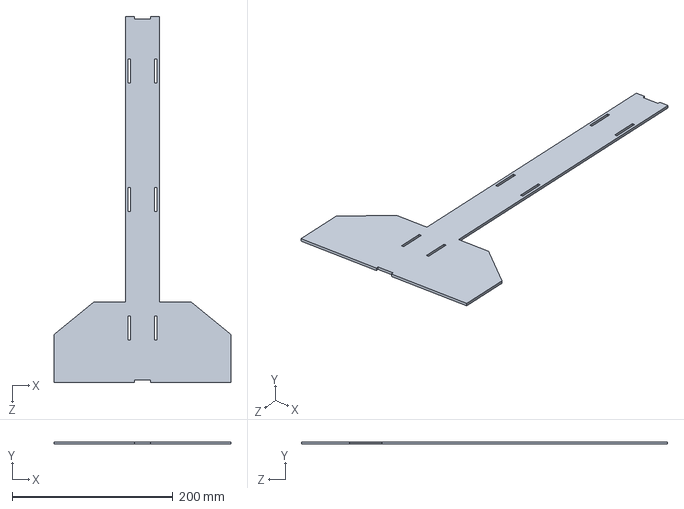
[picture p91: CAD file, 2021-06-23]
Design Model/Autocad/Khungcua_vachhongtrai.SLDPRT
220.0 x 3.00 x 456.0 mm
