CodeMarker01/do-an-1-b/Design Model/Autocad/Khungcua_vachhongphai.SLDPRT

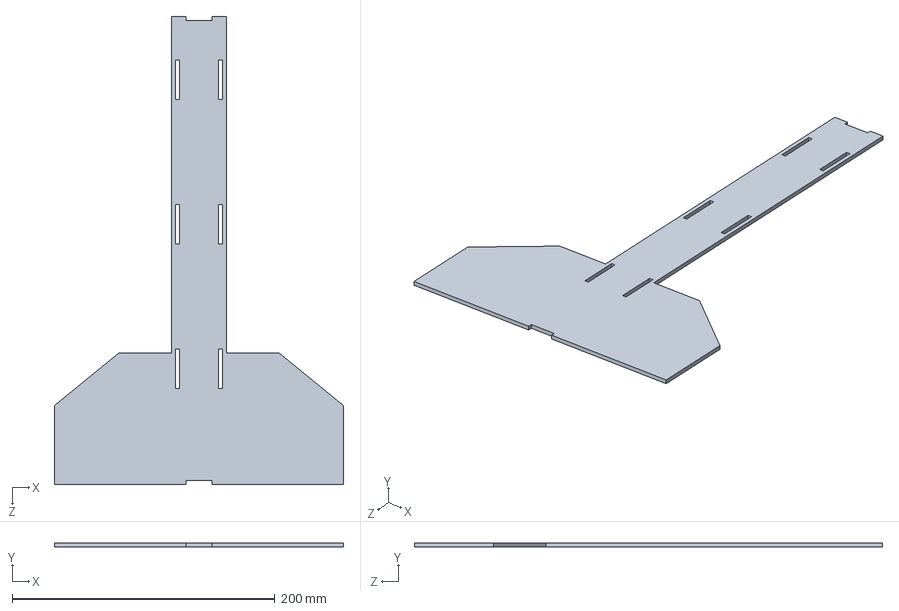
[picture p92: CAD file, 2021-06-23]
Design Model/Autocad/Khungcua_vachhongphai.SLDPRT
220.0 x 3.00 x 356.0 mm
