CodeMarker01/do-an-1-b/Embedded/Code/DS1307_ESP32/DS1307_ESP32.ino

// Date and time functions using a DS1307 RTC connected via I2C and Wire lib
#include "RTClib.h"
RTC_DS1307 rtc;
char daysOfTheWeek[7][12] = {"Sunday", "Monday", "Tuesday", "Wednesday", "Thursday", "Friday", "Saturday"};

void setup () 
{
  Serial.begin(9600);
//  if (! rtc.begin())
//  {
//    Serial.println("Couldn't find RTC");
//    Serial.flush();
//    abort();
//  }
  if(!rtc.begin())
  {
    Serial.println("ERROR");
    return;
  }

  if (! rtc.isrunning()) 
  {
    Serial.println("RTC is NOT running, let's set the time!");
    rtc.adjust(DateTime(F(__DATE__), F(__TIME__)));
     //rtc.adjust(DateTime(2021, 5, 3, 14, 38, 0)); // YEAR/MON/DAY/HOUR/MINUTE/SECOND
  }
}

void loop () 
{
    DateTime now = rtc.now();
    Serial.print(now.year(), DEC);
    Serial.print('/');
    Serial.print(now.month(), DEC);
    Serial.print('/');
    Serial.print(now.day(), DEC);
    Serial.print(" (");
    Serial.print(daysOfTheWeek[now.dayOfTheWeek()]);
    Serial.print(") ");
    Serial.print(now.hour(), DEC);
    Serial.print(':');
    Serial.print(now.minute(), DEC);
    Serial.print(':');
    Serial.print(now.second(), DEC);
    Serial.println();
    delay(1000);
}
