CodeMarker01/do-an-1-b/Embedded/Code/RFID_ESP32/RFID_ESP32.ino

#include <SPI.h>
#include <MFRC522.h>
#define RST_PIN      10  //26
#define SS_PIN       9 // 5
MFRC522 mfrc522(SS_PIN, RST_PIN);
byte a[]= {0XC9,0XA9};
void setup() 
{
Serial.begin(9600);
SPI.begin();
mfrc522.PCD_Init();
Serial.println("Khởi tạo thành công, đang chờ đọc thẻ…");
}
void loop()
{
  if ( ! mfrc522.PICC_IsNewCardPresent()) 
  {
  return;
  }
  if ( ! mfrc522.PICC_ReadCardSerial()) 
  {
  return;
  }
  Serial.println("ID thẻ: ");
  for (byte i = 0; i < 5; i++)
  {
    //Serial.print(mfrc522.uid.uidByte[i] < 0x10 ? " 0 ": " ");
    Serial.print(mfrc522.uid.uidByte[i], HEX);
  }
  Serial.println("");
  mfrc522.PICC_HaltA();
  mfrc522.PCD_StopCrypto1();
  
  if(mfrc522.uid.uidByte[0] == a[0])
  {
    Serial.println("ON");
  } else Serial.println("OFF");

}
